yangosoft/stm32f103c8-board/code/freertos_stm32f103rb6/inc/a.h

/*
#include <taskcpp.h>


#ifndef ITHREAD_H
#define ITHREAD_H



class TaskClass : public TaskBase {
public:
  TaskClass(char const*name, unsigned portBASE_TYPE priority,
           unsigned portSHORT stackDepth=configMINIMAL_STACK_SIZE);
  virtual void task() = 0;
  
};


#endif*/
