yangosoft/stm32f103c8-board/code/freertos_stm32f103rb6/src/a.cpp

#include "a.h"





/*
  TaskClass::TaskClass(char const*name, unsigned portBASE_TYPE priority,
           unsigned portSHORT stackDepth=configMINIMAL_STACK_SIZE) {
    xTaskCreate(&taskfun, (signed char*)name, stackDepth, this, priority, &handle);
  }
  virtual void task() = 0;
  
  
  static void taskfun(void* parm) {
    static_cast<TaskClass> (parm)->task();

    while(1)
      vTaskDelay(10000);

  }*/
